sish1ka/analog-signal-conditioning-pcb/LTspice/Analog-Signal-Conditioning-PCB.asc

C1: cap; 10n
R1: res; 10k
R2: res; 20k
R3: res; 10k
U1: UniversalOpAmp2
V1: voltage; SINE(0 50m 60)
V2: voltage; 5
V3: voltage; 5
Named nets: v+, v-, 0, out
